BananerCatter/keeb-colon-three/Journal/img/Pasted image.png

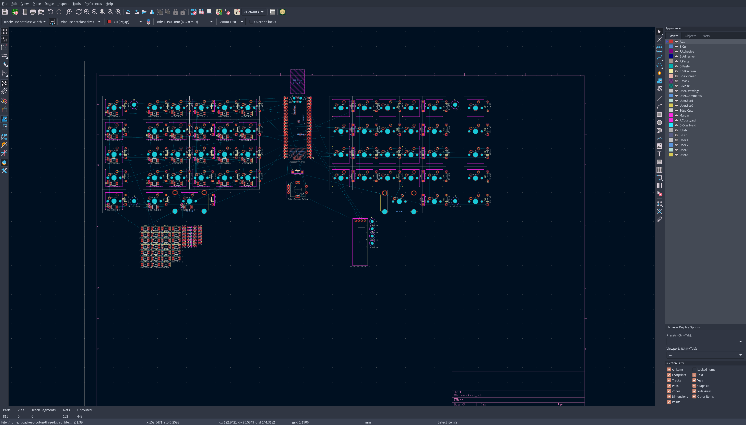
Journal/img/Pasted image.png
